cherrypi11411/OpticalFlowBoard/arduino-code/PMW3901.cpp

/* PMW3901 Arduino driver
   Copyright (c) 2017 Bitcraze AB

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
   THE SOFTWARE IS PROVIDED "AS IS", WITHOUT WARRANTY OF ANY KIND, EXPRESS OR
   IMPLIED, INCLUDING BUT NOT LIMITED TO THE WARRANTIES OF MERCHANTABILITY,
   FITNESS FOR A PARTICULAR PURPOSE AND NONINFRINGEMENT. IN NO EVENT SHALL THE
   AUTHORS OR COPYRIGHT HOLDERS BE LIABLE FOR ANY CLAIM, DAMAGES OR OTHER
   LIABILITY, WHETHER IN AN ACTION OF CONTRACT, TORT OR OTHERWISE, ARISING FROM,
   OUT OF OR IN CONNECTION WITH THE SOFTWARE OR THE USE OR OTHER DEALINGS IN THE
   SOFTWARE.
*/
#include <Arduino.h>
#include <SPI.h>
#include "PMW3901.h"

PMW3901::PMW3901(uint8_t cspin)
  : _cs(cspin)
{ }

boolean PMW3901::begin(void) {
  // Setup SPI port
  SPI.begin();
  pinMode(_cs, OUTPUT);
  SPI.beginTransaction(SPISettings(2000000, MSBFIRST, SPI_MODE3));

  // Make sure the SPI bus is reset
  digitalWrite(_cs, HIGH);
  delay(1);
  digitalWrite(_cs, LOW);
  delay(1);
  digitalWrite(_cs, HIGH);
  delay(1);

  SPI.endTransaction();

  // Power on reset
  registerWrite(0x3A, 0x5A);
  delay(5);

  // Test the SPI communication, checking chipId and inverse chipId
  uint8_t chipId = registerRead(0x00);
  uint8_t dIpihc = registerRead(0x5F);

  if (chipId != 0x49 && dIpihc != 0xB8) return false;

  // Reading the motion registers one time
  registerRead(0x02);
  registerRead(0x03);
  registerRead(0x04);
  registerRead(0x05);
  registerRead(0x06);
  delay(1);

  initRegisters();

  return true;
}

// Functional access

// Low level register access
void PMW3901::registerWrite(uint8_t reg, uint8_t value) {
  reg |= 0x80u;

  SPI.beginTransaction(SPISettings(2000000, MSBFIRST, SPI_MODE3));

  digitalWrite(_cs, LOW);

  delayMicroseconds(50);
  SPI.transfer(reg);
  SPI.transfer(value);
  delayMicroseconds(50);

  digitalWrite(_cs, HIGH);

  SPI.endTransaction();

  delayMicroseconds(200);
}

uint8_t PMW3901::registerRead(uint8_t reg) {
  reg &= ~0x80u;

  SPI.beginTransaction(SPISettings(2000000, MSBFIRST, SPI_MODE3));

  digitalWrite(_cs, LOW);

  delayMicroseconds(50);
  SPI.transfer(reg);
  delayMicroseconds(50);
  uint8_t value = SPI.transfer(0);
  delayMicroseconds(200);

  digitalWrite(_cs, HIGH);

  delayMicroseconds(200);

  SPI.endTransaction();

  return value;
}

// Performance optimisation registers
void PMW3901::initRegisters()
{
  registerWrite(0x7F, 0x00);
  registerWrite(0x61, 0xAD);
  registerWrite(0x7F, 0x03);
  registerWrite(0x40, 0x00);
  registerWrite(0x7F, 0x05);
  registerWrite(0x41, 0xB3);
  registerWrite(0x43, 0xF1);
  registerWrite(0x45, 0x14);
  registerWrite(0x5B, 0x32);
  registerWrite(0x5F, 0x34);
  registerWrite(0x7B, 0x08);
  registerWrite(0x7F, 0x06);
  registerWrite(0x44, 0x1B);
  registerWrite(0x40, 0xBF);
  registerWrite(0x4E, 0x3F);
  registerWrite(0x7F, 0x08);
  registerWrite(0x65, 0x20);
  registerWrite(0x6A, 0x18);
  registerWrite(0x7F, 0x09);
  registerWrite(0x4F, 0xAF);
  registerWrite(0x5F, 0x40);
  registerWrite(0x48, 0x80);
  registerWrite(0x49, 0x80);
  registerWrite(0x57, 0x77);
  registerWrite(0x60, 0x78);
  registerWrite(0x61, 0x78);
  registerWrite(0x62, 0x08);
  registerWrite(0x63, 0x50);
  registerWrite(0x7F, 0x0A);
  registerWrite(0x45, 0x60);
  registerWrite(0x7F, 0x00);
  registerWrite(0x4D, 0x11);
  registerWrite(0x55, 0x80);
  registerWrite(0x74, 0x1F);
  registerWrite(0x75, 0x1F);
  registerWrite(0x4A, 0x78);
  registerWrite(0x4B, 0x78);
  registerWrite(0x44, 0x08);
  registerWrite(0x45, 0x50);
  registerWrite(0x64, 0xFF);
  registerWrite(0x65, 0x1F);
  registerWrite(0x7F, 0x14);
  registerWrite(0x65, 0x60);
  registerWrite(0x66, 0x08);
  registerWrite(0x63, 0x78);
  registerWrite(0x7F, 0x15);
  registerWrite(0x48, 0x58);
  registerWrite(0x7F, 0x07);
  registerWrite(0x41, 0x0D);
  registerWrite(0x43, 0x14);
  registerWrite(0x4B, 0x0E);
  registerWrite(0x45, 0x0F);
  registerWrite(0x44, 0x42);
  registerWrite(0x4C, 0x80);
  registerWrite(0x7F, 0x10);
  registerWrite(0x5B, 0x02);
  registerWrite(0x7F, 0x07);
  registerWrite(0x40, 0x41);
  registerWrite(0x70, 0x00);

  delay(100);
  registerWrite(0x32, 0x44);
  registerWrite(0x7F, 0x07);
  registerWrite(0x40, 0x40);
  registerWrite(0x7F, 0x06);
  registerWrite(0x62, 0xf0);
  registerWrite(0x63, 0x00);
  registerWrite(0x7F, 0x0D);
  registerWrite(0x48, 0xC0);
  registerWrite(0x6F, 0xd5);
  registerWrite(0x7F, 0x00);
  registerWrite(0x5B, 0xa0);
  registerWrite(0x4E, 0xA8);
  registerWrite(0x5A, 0x50);
  registerWrite(0x40, 0x80);
}
